PaulKlinger/tinypc/TinyPC/schematic/schematic.sch

## EAGLE design TinyPC/schematic/schematic.sch (2019-03-21)

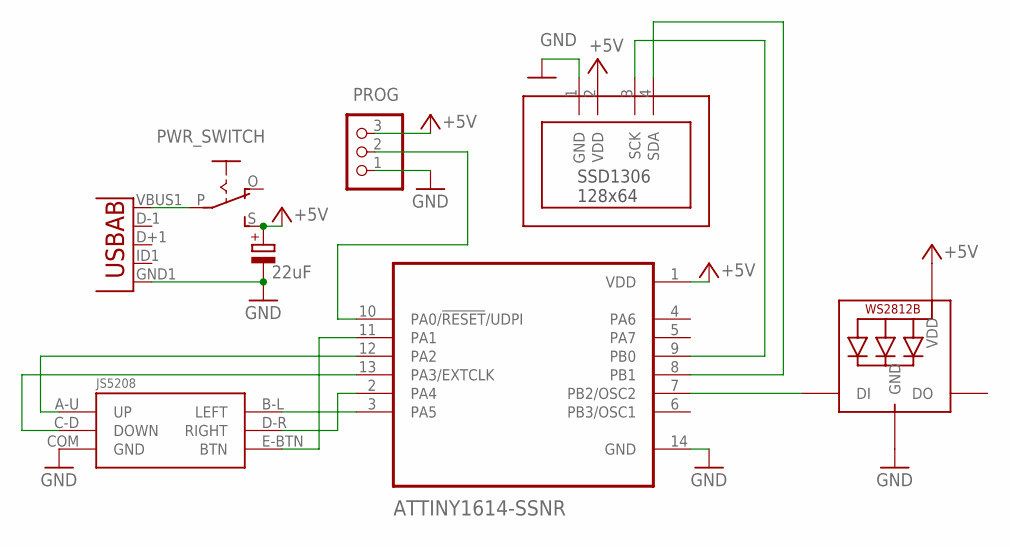
[picture p26: schematic schematic.sch]

Parts:
C2: 22uF; E2-4
LED1: WS2812B5050; WS2812B
PROG: PINHD-1X3; 1X03
PWR_SWITCH: EG1218S; EG1218
U1: ATTINY1614-SSNR; SOIC127P600X175-14N
U2: USB-THROUGH; USB-MICRO-THROUGH
U$1: JS5208; JS5208_PKG
U$2: SSD1306_128X64_OLEDPINHEAD; 1X04-CLEANBIG

Connections:
+5V: C2.+, LED1.1-VDD (VDD), PROG.3, PWR_SWITCH.S, U1.1 (VDD), U$2.2 (VDD)
GND: C2.-, LED1.3-GND (GND), PROG.1, U1.14 (GND), U2.GND1 (GND), U$1.COM (GND), U$2.1 (GND)
unnamed: PWR_SWITCH.P, U2.VBUS1 (VBUS)
unnamed: PROG.2, U1.10 (PA0/!RESET!/UDPI)
unnamed: U1.11 (PA1), U$1.E-BTN (BTN)
unnamed: U1.2 (PA4), U$1.D-R (RIGHT)
unnamed: U1.3 (PA5), U$1.B-L (LEFT)
unnamed: U1.12 (PA2), U$1.A-U (UP)
unnamed: U1.13 (PA3/EXTCLK), U$1.C-D (DOWN)
unnamed: LED1.4-DIN (DI), U1.7 (PB2/OSC2)
unnamed: U1.8 (PB1), U$2.4 (SDA)
unnamed: U1.9 (PB0), U$2.3 (SCK)
