PaulKlinger/tinypc/code/config.h

/* 
 * File:   config.h
 * Author: Paul
 *
 * Created on July 17, 2019, 8:42 PM
 */

#ifndef CONFIG_H
#define	CONFIG_H

#ifdef	__cplusplus
extern "C" {
#endif

// shows that this is the version that runs on the tiny thinkpad instead of
// the gaming pc, changes strings and LED intensity
#define THINKTINY 


#ifdef	__cplusplus
}
#endif

#endif	/* CONFIG_H */
